markadev/AppleII-VGA/pico/hires_rgb_color_patterns.h

#pragma once

// clang-format off
#define _PIXELS(color1, color2) ((uint32_t)(color1) | ((uint32_t)(color2) << 16))
static uint32_t hires_rgb_color_patterns[2 * 256] = {
    // Even byte pixels
    /* 0b00000000 */ _PIXELS(0x000, 0x000),
    /* 0b00000001 */ _PIXELS(0x000, 0x000),
    /* 0b00000010 */ _PIXELS(0x000, 0x000),
    /* 0b00000011 */ _PIXELS(0x000, 0x000),
    /* 0b00000100 */ _PIXELS(0x000, 0x000),
    /* 0b00000101 */ _PIXELS(0x000, 0x000),
    /* 0b00000110 */ _PIXELS(0x000, 0x000),
    /* 0b00000111 */ _PIXELS(0x000, 0x000),
    /* 0b00001000 */ _PIXELS(0x103, 0x000),
    /* 0b00001001 */ _PIXELS(0x104, 0x000),
    /* 0b00001010 */ _PIXELS(0x114, 0x000),
    /* 0b00001011 */ _PIXELS(0x11c, 0x000),
    /* 0b00001100 */ _PIXELS(0x1e1, 0x000),
    /* 0b00001101 */ _PIXELS(0x1e2, 0x000),
    /* 0b00001110 */ _PIXELS(0x1a9, 0x000),
    /* 0b00001111 */ _PIXELS(0x1ff, 0x000),
    /* 0b00010000 */ _PIXELS(0x000, 0x04e),
    /* 0b00010001 */ _PIXELS(0x04e, 0x04e),
    /* 0b00010010 */ _PIXELS(0x026, 0x056),
    /* 0b00010011 */ _PIXELS(0x026, 0x056),
    /* 0b00010100 */ _PIXELS(0x0db, 0x0dd),
    /* 0b00010101 */ _PIXELS(0x0dc, 0x0dd),
    /* 0b00010110 */ _PIXELS(0x0ac, 0x0dd),
    /* 0b00010111 */ _PIXELS(0x0ed, 0x0dd),
    /* 0b00011000 */ _PIXELS(0x14e, 0x14e),
    /* 0b00011001 */ _PIXELS(0x197, 0x14e),
    /* 0b00011010 */ _PIXELS(0x15f, 0x157),
    /* 0b00011011 */ _PIXELS(0x167, 0x157),
    /* 0b00011100 */ _PIXELS(0x1de, 0x19e),
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
    /* 0b11111010 */ _PIXELS(0x1ff, 0x1ff),
    /* 0b11111011 */ _PIXELS(0x1ff, 0x1ff),
    /* 0b11111100 */ _PIXELS(0x1ff, 0x1ff),
    /* 0b11111101 */ _PIXELS(0x1ff, 0x1ff),
    /* 0b11111110 */ _PIXELS(0x1ff, 0x1ff),
    /* 0b11111111 */ _PIXELS(0x1ff, 0x1ff),
};
#undef _PIXELS
