markadev/AppleII-VGA/pico/textfont_iie.c

#include "textfont.h"
#include <pico/platform.h>


#ifdef APPLE_MODEL_IIE
const uint8_t __in_flash("chr_rom") default_character_rom[256 * 8] = {
    //
    // Inverse control (upper) Set
    //

    // Inverse control (upper) character 0x00
    0b01100011,
    0b01011101,
    0b01010101,
    0b01000101,
    0b01100101,
    0b01111101,
    0b01000011,
    0b01111111,

    // Inverse control (upper) character 0x01
    0b01110111,
    0b01101011,
    0b01011101,
    0b01011101,
    0b01000001,
    0b01011101,
    0b01011101,
    0b01111111,

    // Inverse control (upper) character 0x02
    0b01100001,
    0b01011101,
    0b01011101,
    0b01100001,
    0b01011101,
    0b01011101,
    0b01100001,
    0b01111111,

    // Inverse control (upper) character 0x03
    0b01100011,
    0b01011101,
    0b01111101,
    0b01111101,
    0b01111101,
    0b01011101,
    0b01100011,
    0b01111111,

    // Inverse control (upper) character 0x04
    0b01100001,
    0b01011101,
    0b01011101,
    0b01011101,
    0b01011101,
    0b01011101,
    0b01100001,
    0b01111111,

    // Inverse control (upper) character 0x05
    0b01000001,
    0b01111101,
    0b01111101,
    0b01100001,
    0b01111101,
    0b01111101,
    0b01000001,
    0b01111111,

    // Inverse control (upper) character 0x06
    0b01000001,
    0b01111101,
    0b01111101,
    0b01100001,
    0b01111101,
    0b01111101,
    0b01111101,
    0b01111111,

    // Inverse control (upper) character 0x07
    0b01000011,
    0b01111101,
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
    0b00011010,
    0b00000000,
    0b00000000,
    0b00000000,
    0b00000000,
    0b00000000,
    0b00000000,

    // Normal lower character 0xff
    0b00000000,
    0b00101010,
    0b00010100,
    0b00101010,
    0b00010100,
    0b00101010,
    0b00000000,
    0b00000000,
};
#endif
