markadev/AppleII-VGA/pico/textfont.c

#include "textfont.h"

/*
    Character stored in ram like this
        ______0 - INVERSE       / 1 - NORMAL
       | _____0 - NOT FLASHING  / 1 - FLASHING
       ||  ___0 - CAP           / 1 - LOWER
       || |   ___ ASCII Code
       || |  |
    0b 00 0 00000

    for example
    A = 0x41 0b 01 0 00001 Normal Flashing CAP A
    a = 0x61 0b 01 1 00001 Normal Flashing Low A

    Char Memory Map first glyph line
    (CH << 3) = rom address
                Memory                Rom Mapped
    Inverse M = 0x0D = 0b 00 001101 -> 0x0068
    Inverse a = 0x61 = 0b 01 100001 -> 0x0308 // Noflashing Lowercases AltChar
   only, other wise flashing "!" Normal  a = 0xE1 = 0b 11 100001 -> 0x0708

 */
#ifdef APPLE_MODEL_IIE
const uint8_t default_character_rom[256 * 8] = {
    ////////////////////////////
    // Inverse Set (0x00-0x3F)//
    ///////////////////////////

    // Inverse '@ at 0x0000'
    0b00011100,
    0b00100010,
    0b00101010,
    0b00101110,
    0b00101100,
    0b00100000,
    0b00011110,
    0b00000000,

    // Inverse 'A at 0x0008'
    0b00001000,
    0b00010100,
    0b00100010,
    0b00100010,
    0b00111110,
    0b00100010,
    0b00100010,
    0b00000000,

    // Inverse 'B at 0x0010'
    0b00111100,
    0b00100010,
    0b00100010,
    0b00111100,
    0b00100010,
    0b00100010,
    0b00111100,
    0b00000000,

    // Inverse 'C at 0x0018'
    0b00011100,
    0b00100010,
    0b00100000,
    0b00100000,
    0b00100000,
    0b00100010,
    0b00011100,
    0b00000000,

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
    0b00000000,
    0b00000000,
    0b00100010,
    0b00100010,
    0b00100010,
    0b00011110,
    0b00000010,
    0b00011100,

    // Normal 'z at 0x07D0'
    0b00000000,
    0b00000000,
    0b00111110,
    0b00000100,
    0b00001000,
    0b00010000,
    0b00111110,
    0b00000000,

    // Normal '{ at 0x07D8'
    0b00001110,
    0b00011000,
    0b00011000,
    0b00110000,
    0b00011000,
    0b00011000,
    0b00001110,
    0b00000000,

    // Normal '| at 0x07E0'
    0b00001000,
    0b00001000,
    0b00001000,
    0b00001000,
    0b00001000,
    0b00001000,
    0b00001000,
    0b00001000,

    // Normal '} at 0x07E8'
    0b00111000,
    0b00001100,
    0b00001100,
    0b00000110,
    0b00001100,
    0b00001100,
    0b00111000,
    0b00000000,

    // Normal '~ at 0x07F0'
    0b00011010,
    0b00101100,
    0b00000000,
    0b00000000,
    0b00000000,
    0b00000000,
    0b00000000,
    0b00000000,

    // Normal 'check pattern at 0x07F8'
    0b00000000,
    0b00101010,
    0b00010100,
    0b00101010,
    0b00010100,
    0b00101010,
    0b00000000,
    0b00000000,
};
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
