markadev/AppleII-VGA/pico/buffers.h

#pragma once

#include <stdint.h>
#include <stdbool.h>


enum {
    SOFTSW_TEXT_MODE = 0x01,
    SOFTSW_MIX_MODE = 0x02,
    SOFTSW_HIRES_MODE = 0x04,
    SOFTSW_MODE_MASK = 0x07,
    SOFTSW_PAGE_2 = 0x08,
};

enum {
    VIDEO7_MODE_140x192 = 0,
    VIDEO7_MODE_160x192 = 1,
    VIDEO7_MODE_MIX = 2,
    VIDEO7_MODE_560x192 = 3,
};

extern volatile uint32_t soft_switches;
extern volatile uint32_t soft_video7_mode;
extern volatile bool soft_80col;
extern volatile bool soft_80store;
extern volatile bool soft_altcharset;
extern volatile bool soft_dhires;
extern volatile bool soft_monochrom;
extern volatile bool soft_ramwrt;

extern volatile bool soft_scanline_emulation;
extern volatile bool soft_force_alt_textcolor;
extern volatile bool soft_smooth_hires;

#define CHARACTER_ROM_SIZE 2048

extern uint8_t character_rom[CHARACTER_ROM_SIZE];

extern uint8_t main_memory[24 * 1024];
extern uint8_t aux_memory[24 * 1024];
extern uint8_t *text_mainmem_page1;
extern uint8_t *text_mainmem_page2;
extern uint8_t *text_auxmem_page1;
extern uint8_t *text_auxmem_page2;
extern uint8_t *hires_mainmem_page1;
extern uint8_t *hires_mainmem_page2;
extern uint8_t *hires_auxmem_page1;
extern uint8_t *hires_auxmem_page2;


static inline bool is_page2_display_enabled() {
    return ((soft_switches & SOFTSW_PAGE_2) && !soft_80store);
}
