markadev/AppleII-VGA/pico/hires_dot_patterns.h

#pragma once

// clang-format off
#include <stdint.h>

// Mapping of a hires video byte to 14 half-pixel dots.
// Bits are displayed from LSB to MSB.
static uint16_t hires_dot_patterns[256] = {
    0x0000,0x0003,0x000c,0x000f,0x0030,0x0033,0x003c,0x003f,
    0x00c0,0x00c3,0x00cc,0x00cf,0x00f0,0x00f3,0x00fc,0x00ff,
    0x0300,0x0303,0x030c,0x030f,0x0330,0x0333,0x033c,0x033f,
    0x03c0,0x03c3,0x03cc,0x03cf,0x03f0,0x03f3,0x03fc,0x03ff,
    0x0c00,0x0c03,0x0c0c,0x0c0f,0x0c30,0x0c33,0x0c3c,0x0c3f,
    0x0cc0,0x0cc3,0x0ccc,0x0ccf,0x0cf0,0x0cf3,0x0cfc,0x0cff,
    0x0f00,0x0f03,0x0f0c,0x0f0f,0x0f30,0x0f33,0x0f3c,0x0f3f,
    0x0fc0,0x0fc3,0x0fcc,0x0fcf,0x0ff0,0x0ff3,0x0ffc,0x0fff,
    0x3000,0x3003,0x300c,0x300f,0x3030,0x3033,0x303c,0x303f,
    0x30c0,0x30c3,0x30cc,0x30cf,0x30f0,0x30f3,0x30fc,0x30ff,
    0x3300,0x3303,0x330c,0x330f,0x3330,0x3333,0x333c,0x333f,
    0x33c0,0x33c3,0x33cc,0x33cf,0x33f0,0x33f3,0x33fc,0x33ff,
    0x3c00,0x3c03,0x3c0c,0x3c0f,0x3c30,0x3c33,0x3c3c,0x3c3f,
    0x3cc0,0x3cc3,0x3ccc,0x3ccf,0x3cf0,0x3cf3,0x3cfc,0x3cff,
    0x3f00,0x3f03,0x3f0c,0x3f0f,0x3f30,0x3f33,0x3f3c,0x3f3f,
    0x3fc0,0x3fc3,0x3fcc,0x3fcf,0x3ff0,0x3ff3,0x3ffc,0x3fff,
    0x0000,0x0006,0x0018,0x001e,0x0060,0x0066,0x0078,0x007e,
    0x0180,0x0186,0x0198,0x019e,0x01e0,0x01e6,0x01f8,0x01fe,
    0x0600,0x0606,0x0618,0x061e,0x0660,0x0666,0x0678,0x067e,
    0x0780,0x0786,0x0798,0x079e,0x07e0,0x07e6,0x07f8,0x07fe,
    0x1800,0x1806,0x1818,0x181e,0x1860,0x1866,0x1878,0x187e,
    0x1980,0x1986,0x1998,0x199e,0x19e0,0x19e6,0x19f8,0x19fe,
    0x1e00,0x1e06,0x1e18,0x1e1e,0x1e60,0x1e66,0x1e78,0x1e7e,
    0x1f80,0x1f86,0x1f98,0x1f9e,0x1fe0,0x1fe6,0x1ff8,0x1ffe,
    0x2000,0x2006,0x2018,0x201e,0x2060,0x2066,0x2078,0x207e,
    0x2180,0x2186,0x2198,0x219e,0x21e0,0x21e6,0x21f8,0x21fe,
    0x2600,0x2606,0x2618,0x261e,0x2660,0x2666,0x2678,0x267e,
    0x2780,0x2786,0x2798,0x279e,0x27e0,0x27e6,0x27f8,0x27fe,
    0x3800,0x3806,0x3818,0x381e,0x3860,0x3866,0x3878,0x387e,
    0x3980,0x3986,0x3998,0x399e,0x39e0,0x39e6,0x39f8,0x39fe,
    0x3e00,0x3e06,0x3e18,0x3e1e,0x3e60,0x3e66,0x3e78,0x3e7e,
    0x3f80,0x3f86,0x3f98,0x3f9e,0x3fe0,0x3fe6,0x3ff8,0x3ffe,
};
