markadev/AppleII-VGA/pico/render.h

#pragma once

#include <stdbool.h>


// Uncomment to enable test pattern generator
// #define RENDER_TEST_PATTERN

extern void render_init();
extern void render_loop();

extern void render_vga_testpattern();

extern void update_text_flasher();
extern void render_text();
extern void render_text_line(unsigned int line, bool force_monocolor);

extern void render_lores();
extern void render_mixed_lores();

extern void generate_hires_tables();
extern void render_hires(bool mixed);
