markadev/AppleII-VGA/pico/colors.h

#pragma once

#include <stdint.h>

extern const uint16_t ntsc_palette[16];
extern const uint16_t ntsc90_palette[16];

extern const uint16_t mono_bg_colors[4];
extern const uint16_t mono_fg_colors[4];
extern uint16_t mono_bg_color;
extern uint16_t mono_fg_color;
